kollero/Geiger-Counter/code/src/lipo.h

#define LIPO_ARRAY_LENGTH 21

static double lipo_ADC_to_percentages[][2]={
{4.2,100},
{4.15,95},
{4.11,90},
{4.08,85},    
{4.02,80},
{3.98,75},
{3.95,70},
{3.91,65},
{3.87,60},
{3.85,55},
{3.84,50},
{3.82,45},
{3.80,40},
{3.79,35},
{3.77,30},
{3.75,25},
{3.73,20},
{3.71,15},
{3.69,10},
{3.61,5},
{3.27,0} //21
};
